tdwgithub/sensor-playground/src/arduino/examples/aqi/credentials.h

#ifndef __CREDENTIALS_H_INCLUDED
#define __CREDENTIALS_H_INCLUDED

//%%%%%%%%%%%%%%%%%%%%%%%%%%%%%%%%%%%%%%%%%%%%%%%%%%%%%%%%%%%%%%%%%%
//%%%%%%%%%%%%%%%%%%%%%%%%%%%%%%%%%%%%%%%%%%%%%%%%%%%%%%%%%%%%%%%%%%
//                WHERE IS YOUR BOARD LOCATED?
//%%%%%%%%%%%%%%%%%%%%%%%%%%%%%%%%%%%%%%%%%%%%%%%%%%%%%%%%%%%%%%%%%%
//%%%%%%%%%%%%%%%%%%%%%%%%%%%%%%%%%%%%%%%%%%%%%%%%%%%%%%%%%%%%%%%%%%
#define HOME                        (1)
#define MOMDAD                      (2)
#define LOCATION                    (HOME)


//%%%%%%%%%%%%%%%%%%%%%%%%%%%%%%%%%%%%%%%%%%%%%%%%%%%%%%%%%%%%%%%%%%
//%%%%%%%%%%%%%%%%%%%%%%%%%%%%%%%%%%%%%%%%%%%%%%%%%%%%%%%%%%%%%%%%%%
//                       WiFi Credentials
//%%%%%%%%%%%%%%%%%%%%%%%%%%%%%%%%%%%%%%%%%%%%%%%%%%%%%%%%%%%%%%%%%%
//%%%%%%%%%%%%%%%%%%%%%%%%%%%%%%%%%%%%%%%%%%%%%%%%%%%%%%%%%%%%%%%%%%
#if (LOCATION==HOME)
    #define NET_SSID          ("YOUR WIFI SSID")
    #define NET_PW            ("YOUR WIFI PASSWORD")
#elif (LOCATION==MOMDAD)
    #define NET_SSID          ("YOUR WIFI SSID")
    #define NET_PW            ("YOUR WIFIPASSWORD")
#endif

//%%%%%%%%%%%%%%%%%%%%%%%%%%%%%%%%%%%%%%%%%%%%%%%%%%%%%%%%%%%%%%%%%%
//%%%%%%%%%%%%%%%%%%%%%%%%%%%%%%%%%%%%%%%%%%%%%%%%%%%%%%%%%%%%%%%%%%
// If you use PUSHOVER for push notifications, edit your credentials
// here.
//%%%%%%%%%%%%%%%%%%%%%%%%%%%%%%%%%%%%%%%%%%%%%%%%%%%%%%%%%%%%%%%%%%
//%%%%%%%%%%%%%%%%%%%%%%%%%%%%%%%%%%%%%%%%%%%%%%%%%%%%%%%%%%%%%%%%%%
#define PUSHOVER_USER         ("YOUR PUSHOVER USER KEY")
#define PUSHOVER_API_TOKEN    ("YOUR PUSHOVER API TOKEN")

//%%%%%%%%%%%%%%%%%%%%%%%%%%%%%%%%%%%%%%%%%%%%%%%%%%%%%%%%%%%%%%%%%%
//%%%%%%%%%%%%%%%%%%%%%%%%%%%%%%%%%%%%%%%%%%%%%%%%%%%%%%%%%%%%%%%%%%
//                   ADAFRUIT.IO CREDENTIALS
//%%%%%%%%%%%%%%%%%%%%%%%%%%%%%%%%%%%%%%%%%%%%%%%%%%%%%%%%%%%%%%%%%%
//%%%%%%%%%%%%%%%%%%%%%%%%%%%%%%%%%%%%%%%%%%%%%%%%%%%%%%%%%%%%%%%%%%
#define AIO_USERNAME          ("YOUR ADAFRUIT.IO USER NAME")
#define AIO_KEY               ("YOUR ADAFRUIT.IO API KEY")


#endif  // __CREDENTIALS_H_INCLUDED
